diegoasanch/light/assets/kicad_readme_project_path.png

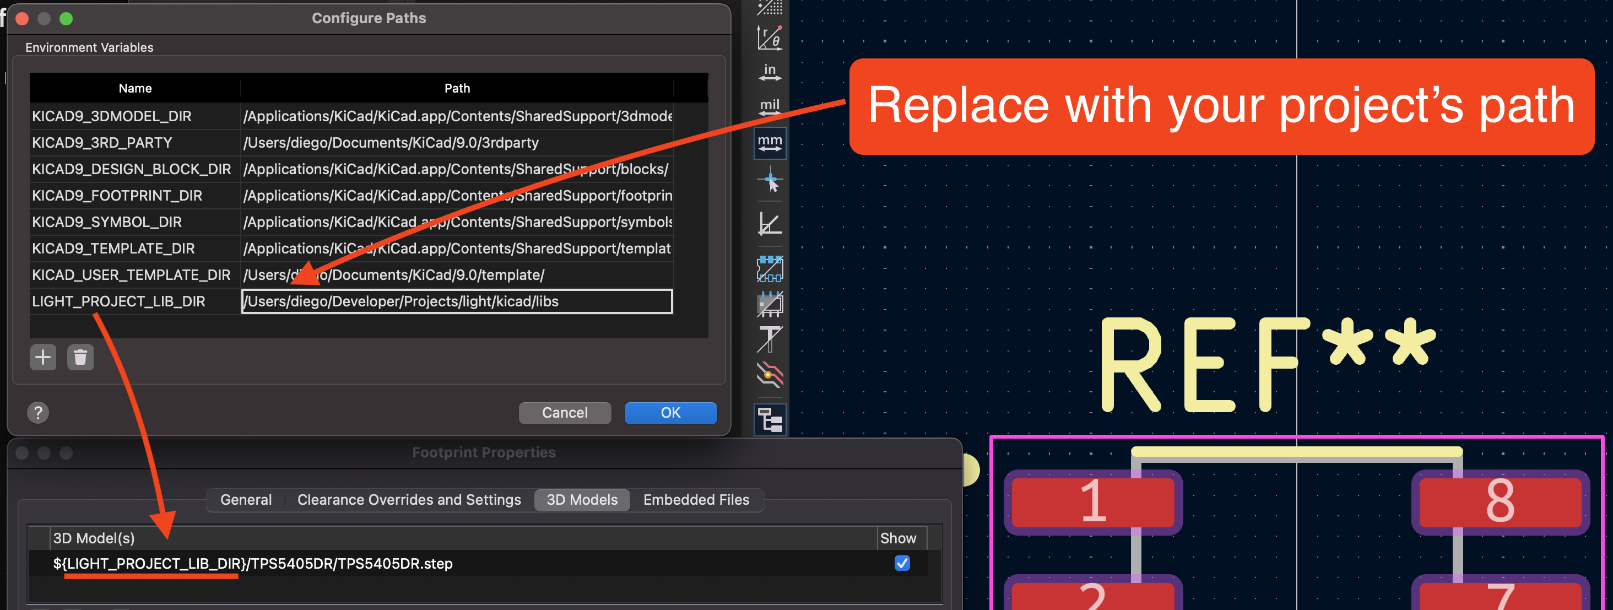
assets/kicad_readme_project_path.png
