diegoasanch/light/assets/light-v1-3d-bottom-iso.png

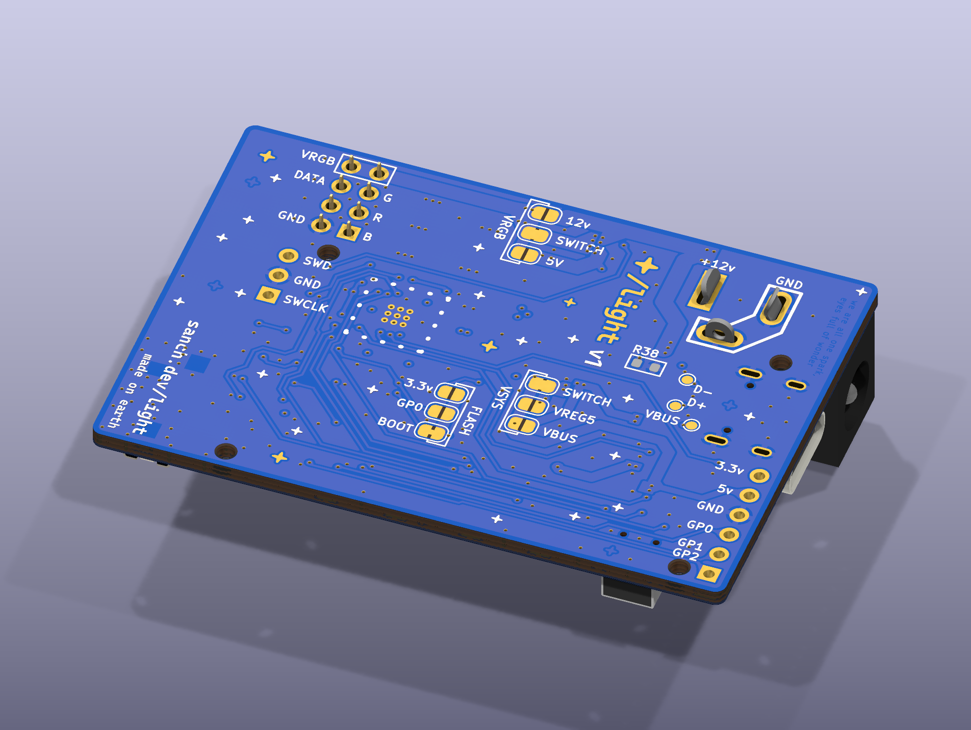
assets/light-v1-3d-bottom-iso.png
