diegoasanch/light/assets/light-v1-3d-bottom.png

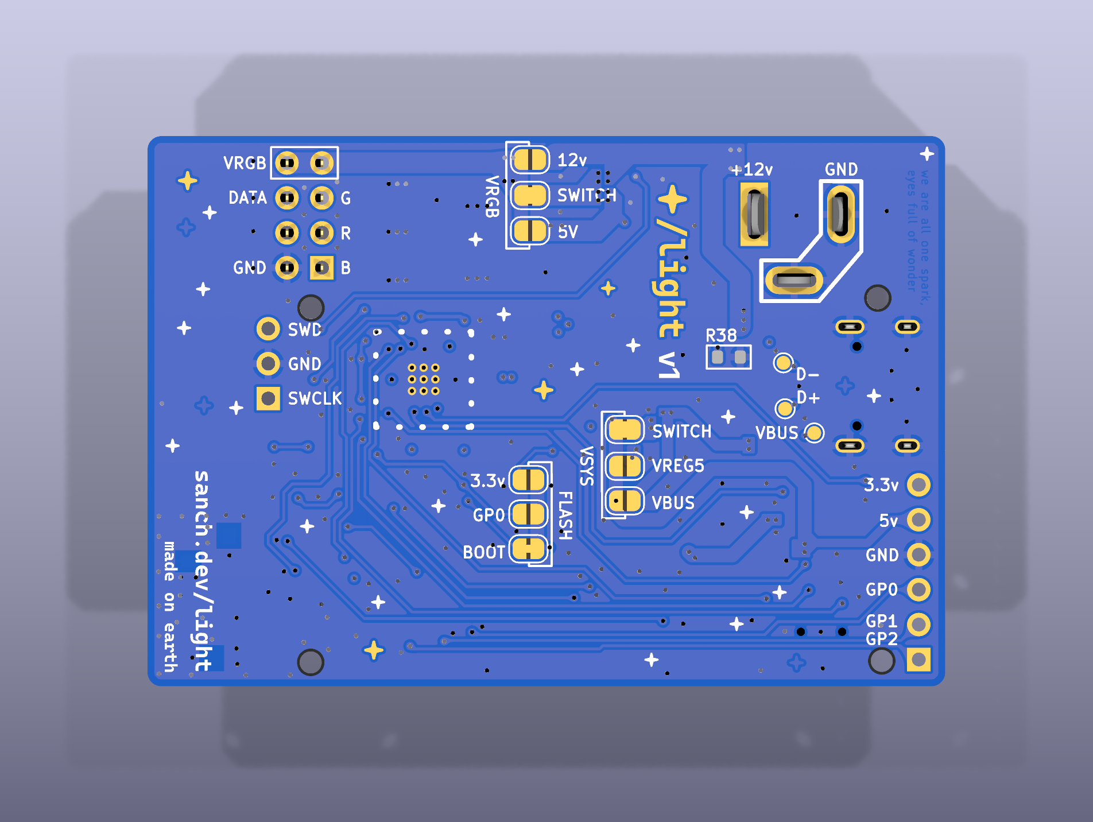
assets/light-v1-3d-bottom.png
