diegoasanch/light/assets/light-v1-3d-top.png

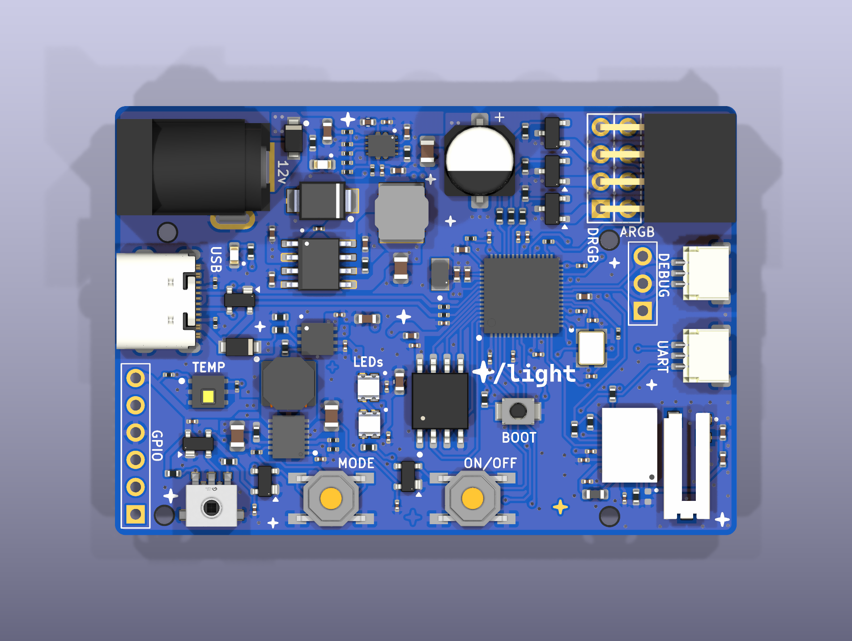
assets/light-v1-3d-top.png
