diegoasanch/light/kicad/reddit_review/rev2/3d-back.png

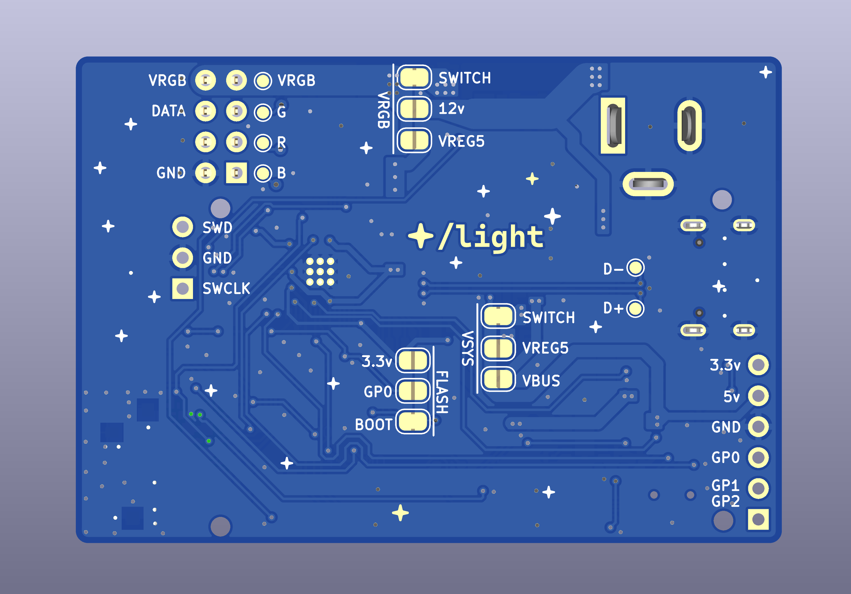
kicad/reddit_review/rev2/3d-back.png
