diegoasanch/light/kicad/reddit_review/rev2/3d-front.png

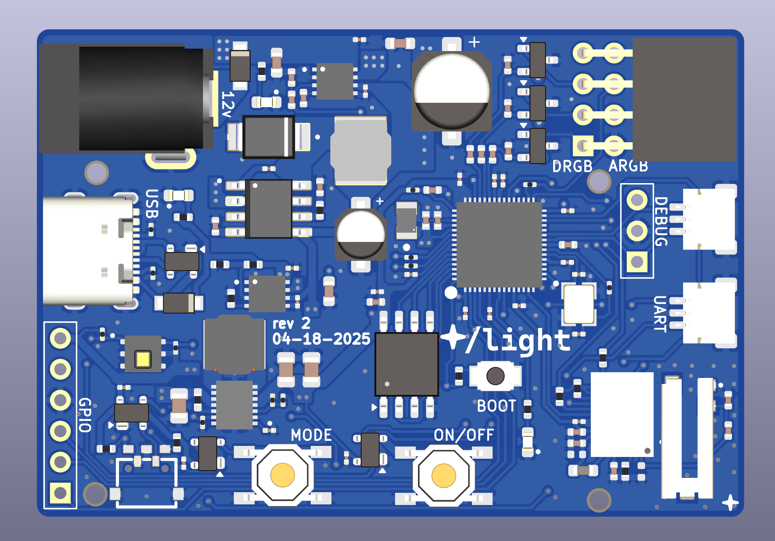
kicad/reddit_review/rev2/3d-front.png
