diegoasanch/light/kicad/reddit_review/rev2/layer-1-filled.png

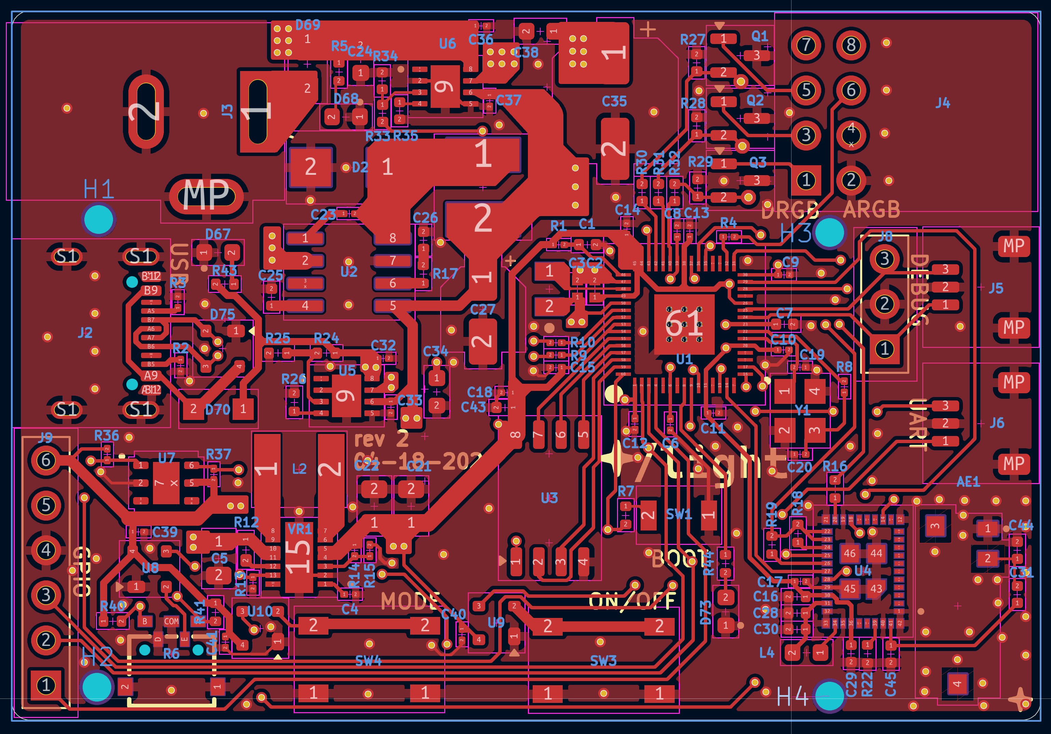
kicad/reddit_review/rev2/layer-1-filled.png
