diegoasanch/light/kicad/reddit_review/rev2/layer-1-only-traces.png

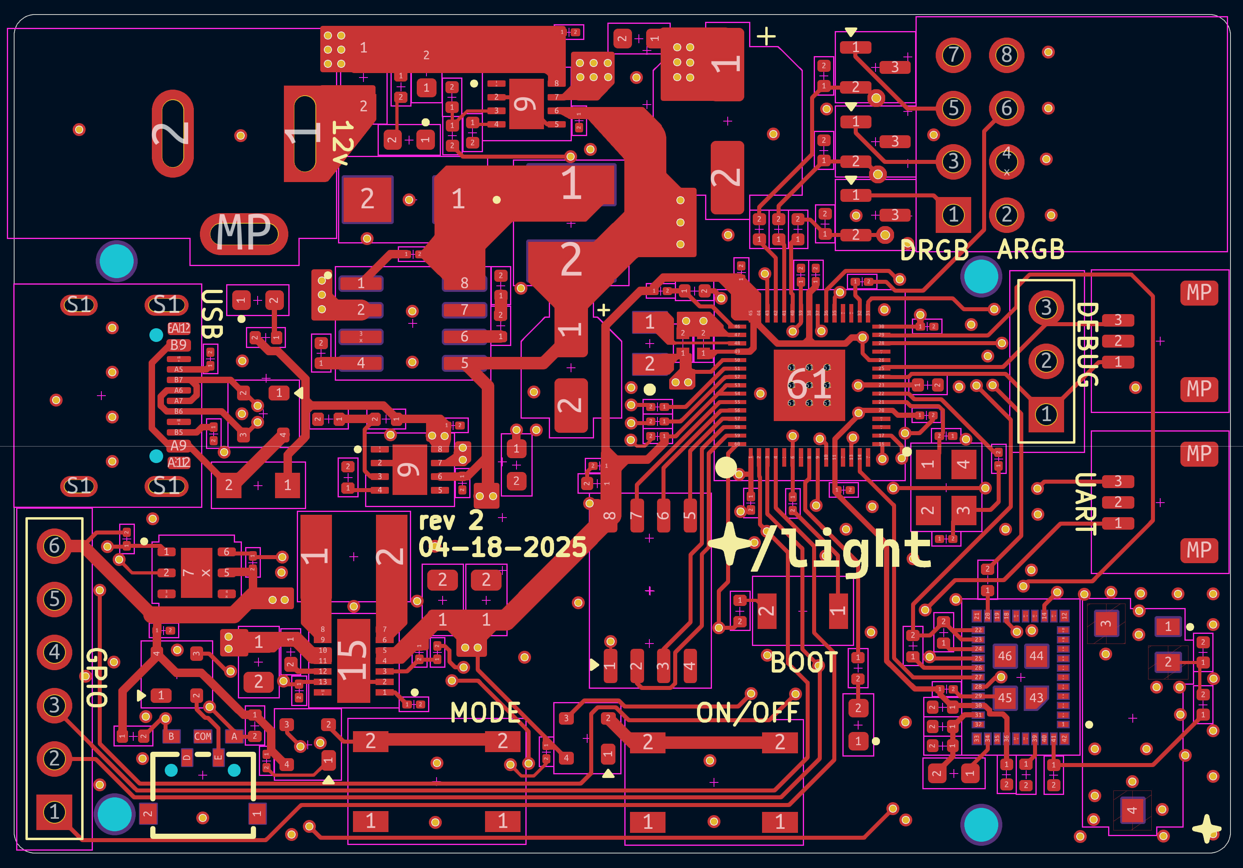
kicad/reddit_review/rev2/layer-1-only-traces.png
