diegoasanch/light/kicad/reddit_review/rev2/layer-2.png

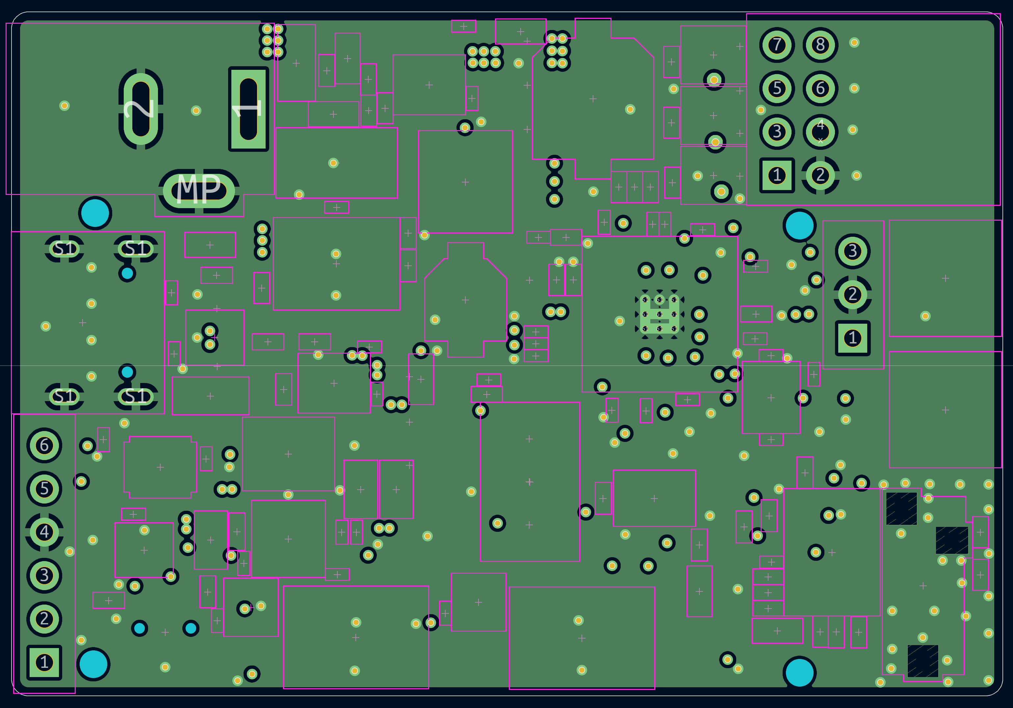
kicad/reddit_review/rev2/layer-2.png
