diegoasanch/light/kicad/reddit_review/rev2/layer-3.png

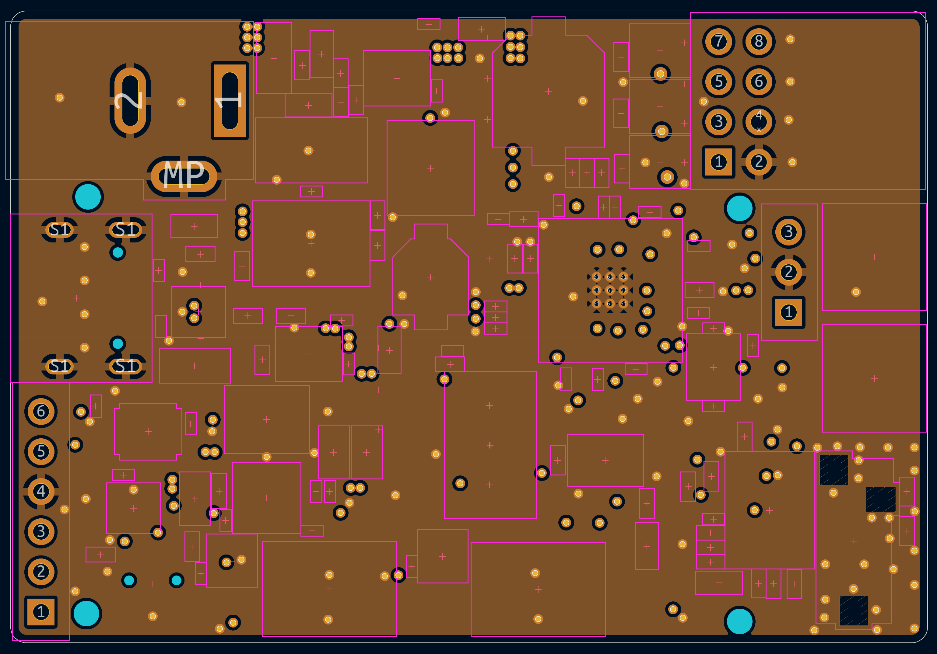
kicad/reddit_review/rev2/layer-3.png
