diegoasanch/light/kicad/reddit_review/rev2/layer-4-filled.png

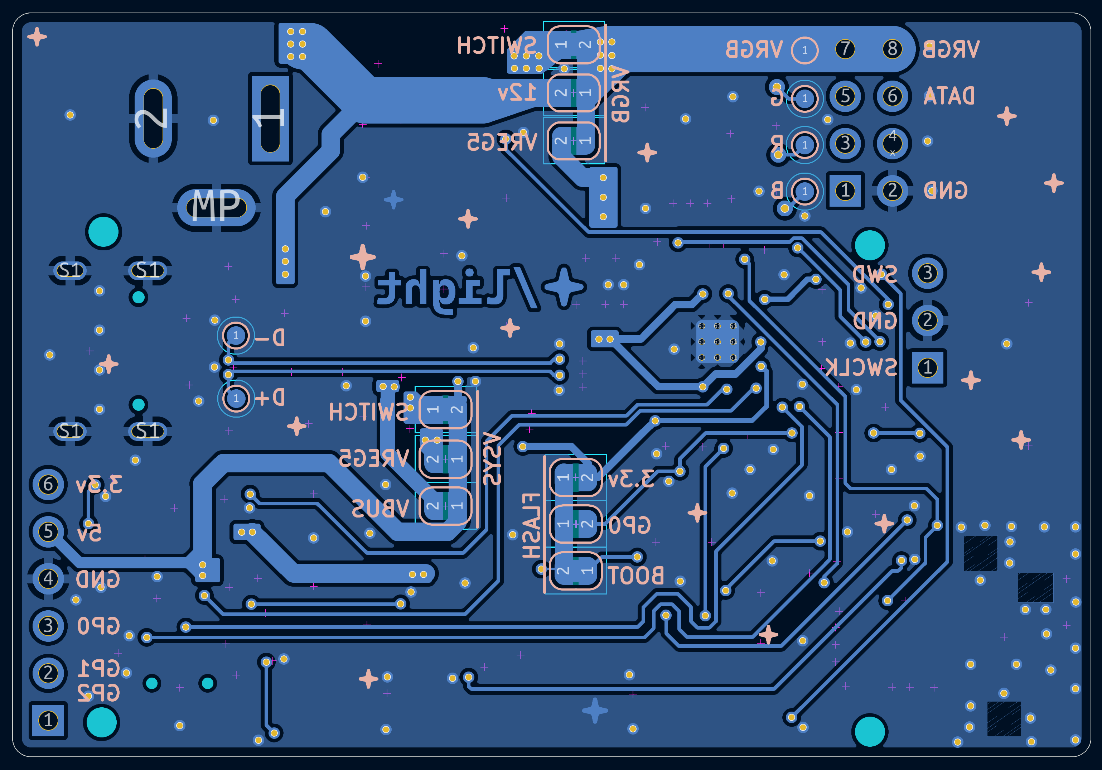
kicad/reddit_review/rev2/layer-4-filled.png
