diegoasanch/light/kicad/reddit_review/rev2/schematics-gpio.png

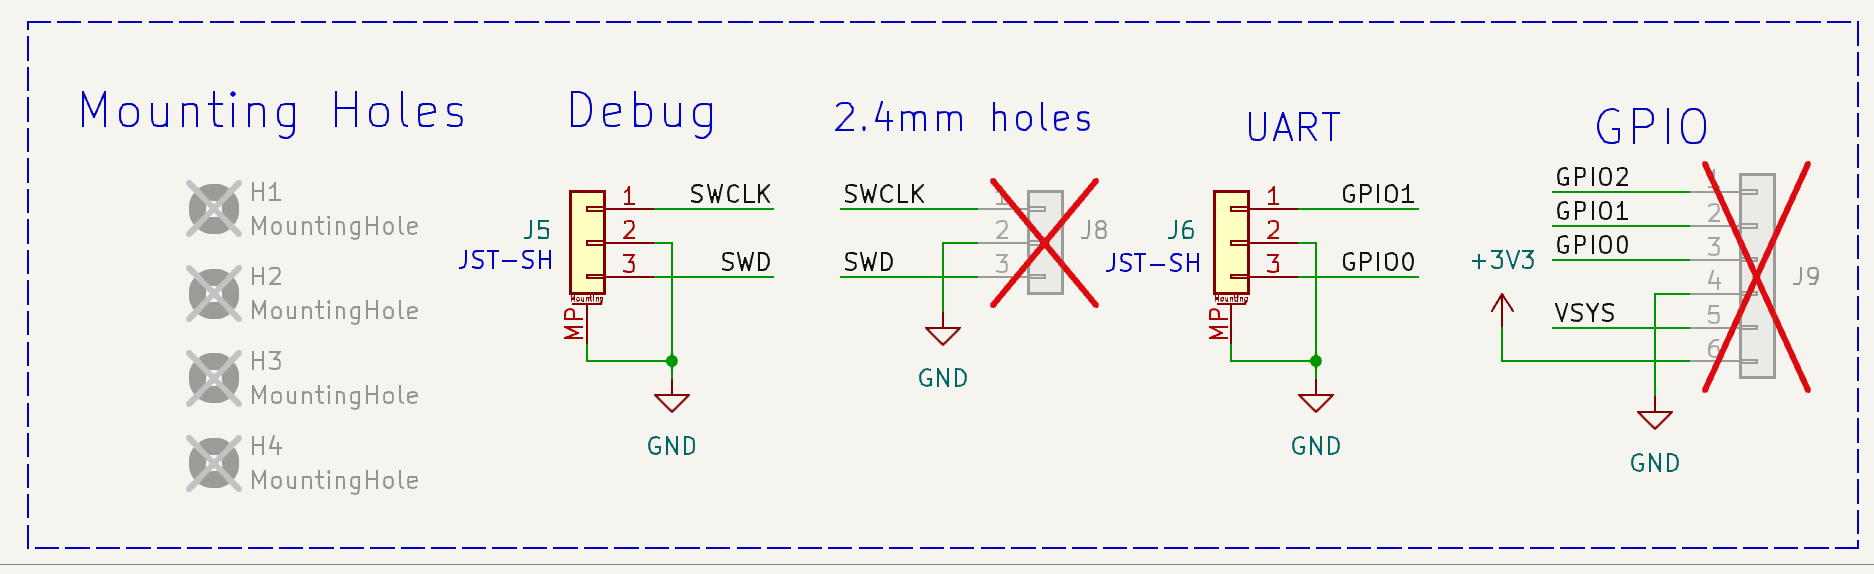
kicad/reddit_review/rev2/schematics-gpio.png
