diegoasanch/light/kicad/reddit_review/rev2/schematics-pwr-data.png

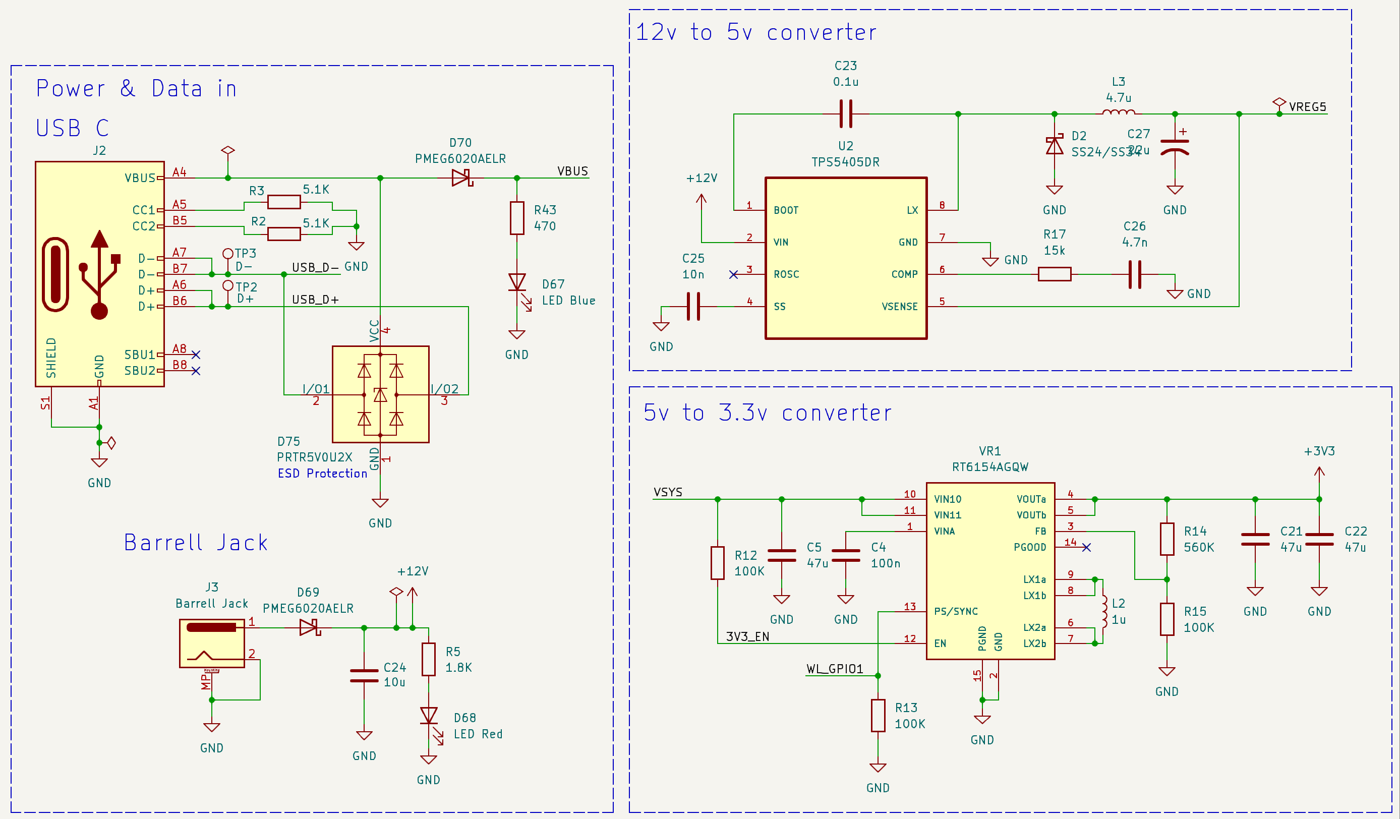
kicad/reddit_review/rev2/schematics-pwr-data.png
