diegoasanch/light/kicad/reddit_review/rev2/schematics-rp.png

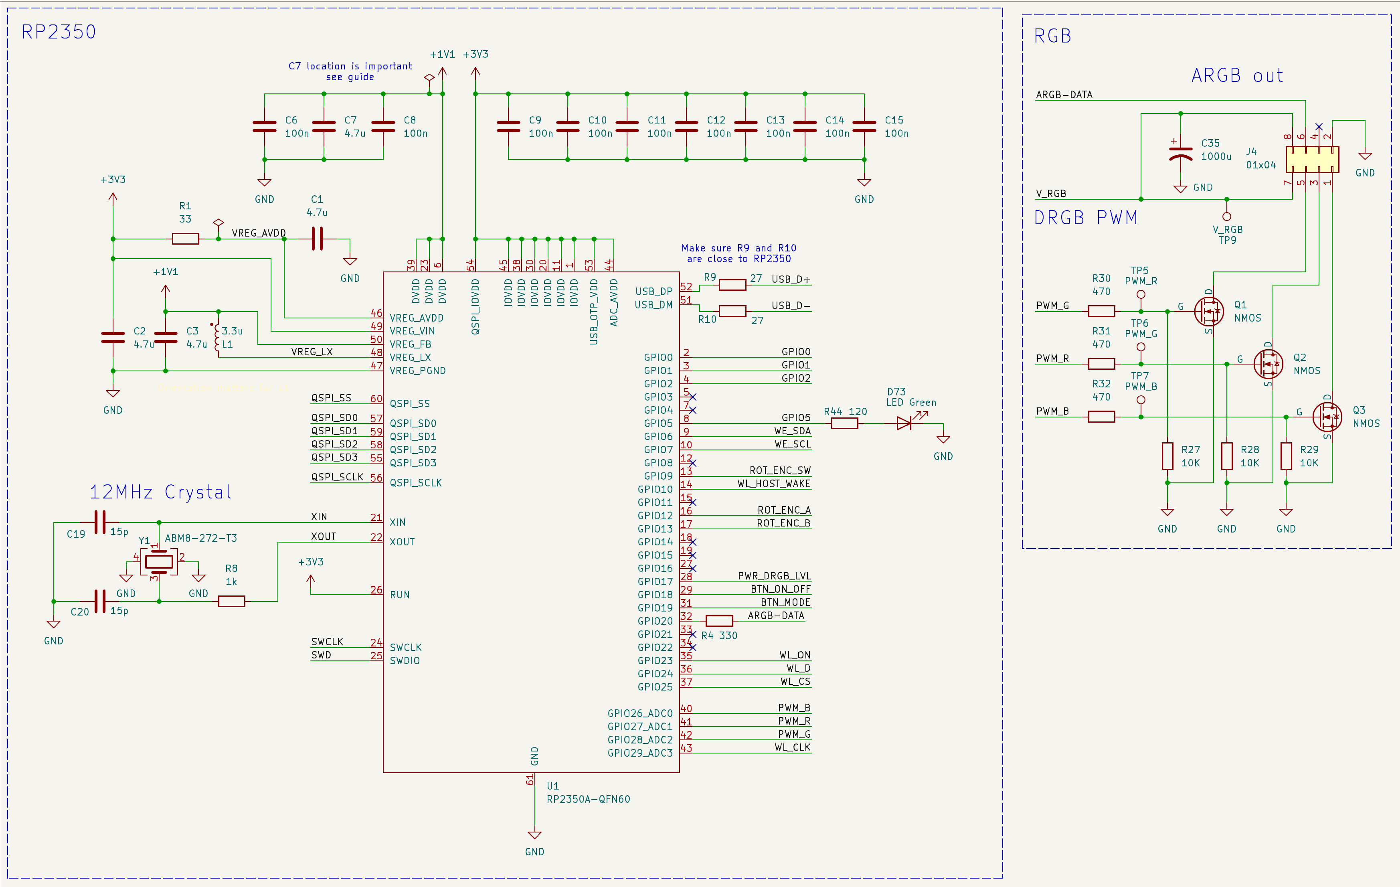
kicad/reddit_review/rev2/schematics-rp.png
